sumanth-kalluri/IRis/Circuit/IRis - Slave PCB Layout.png

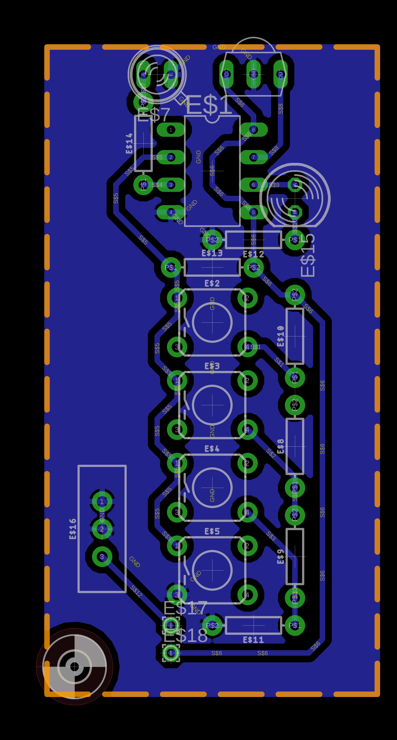
Circuit/IRis - Slave PCB Layout.png
